pjnovas/IoT-NodeMCU/arduino/iot_nodemcu/iot_nodemcu.ino

/*
 *  IoT NodeMCU
 *  To config copy file __config to config, uncomment code and set your configuration
 *
 * Files from Arduino IDE are compiled in alphabetical order so first letter is the order on each file
 *
*/
