pjnovas/IoT-NodeMCU/arduino/iot_nodemcu/z_main.ino

void setup() {
  #ifdef DEBUG
    Serial.begin(115200);
  #endif

  setupEEPROM();
  setupLCD();
  setupRelays();
  setupSensor();
  setupWifi();
  setupWebServer();
}

void loop() {
  loopWebserver();
  loopSensor();
  loopWifi();
}
